freiszel/Nema14-dual-drive-geared-extruder/Images/00_g2d_15_69.png

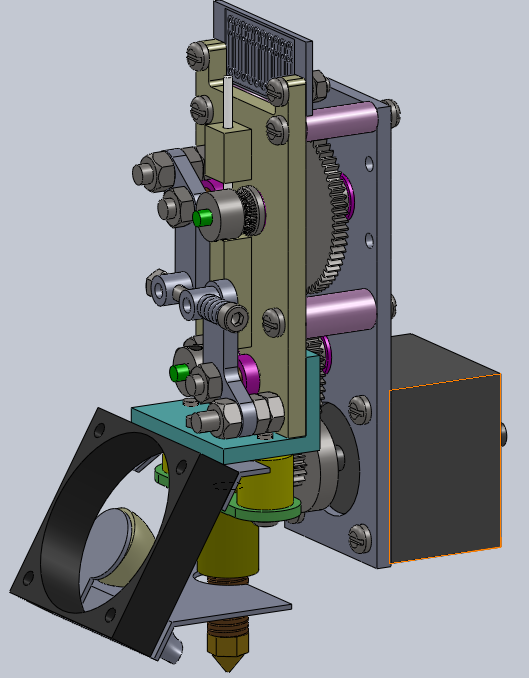
Images/00_g2d_15_69.png
