freiszel/Nema14-dual-drive-geared-extruder/Images/03_GearsMounting.png

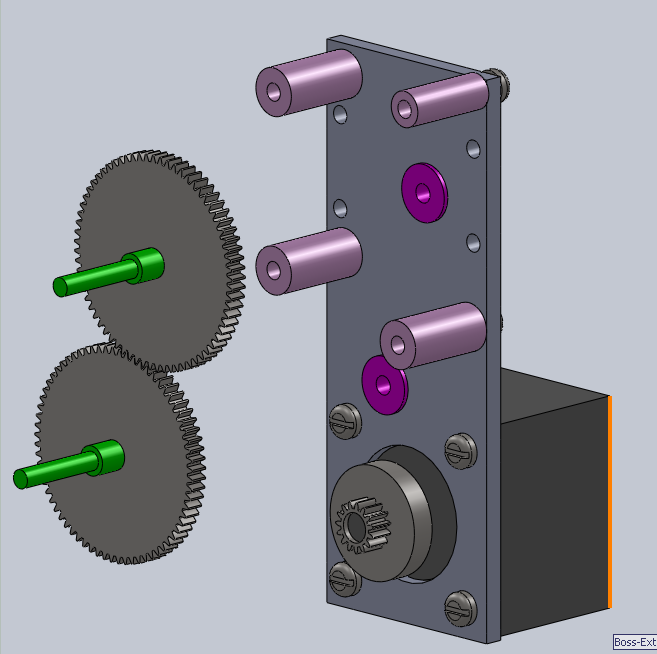
Images/03_GearsMounting.png
