freiszel/Nema14-dual-drive-geared-extruder/Images/04_FrontPlateMounting.png

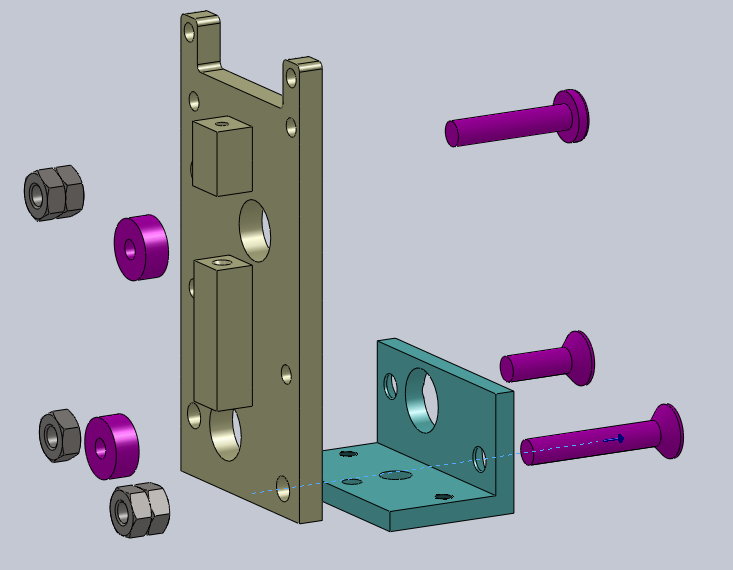
Images/04_FrontPlateMounting.png
