freiszel/Nema14-dual-drive-geared-extruder/Images/05_FrontPlateMounted.png

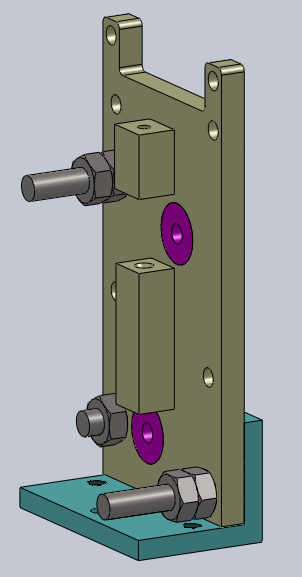
Images/05_FrontPlateMounted.png
