freiszel/Nema14-dual-drive-geared-extruder/Images/06_PressingArmMounting.png

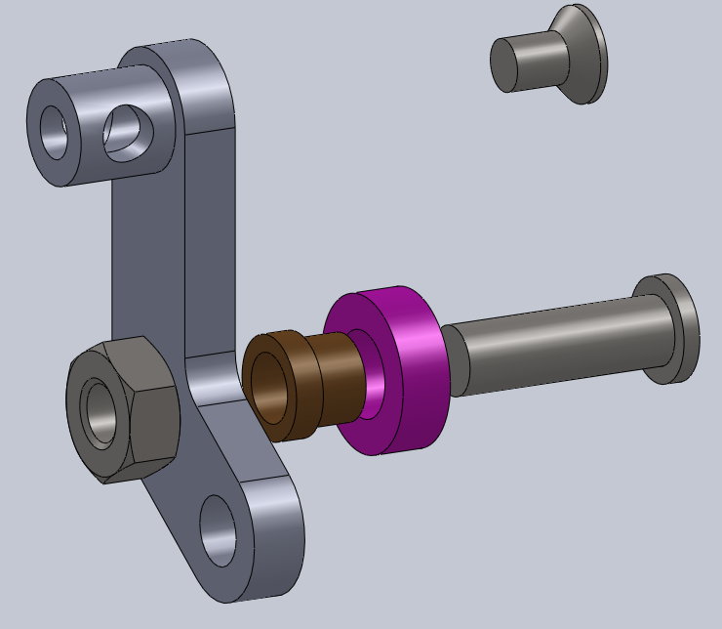
Images/06_PressingArmMounting.png
