freiszel/Nema14-dual-drive-geared-extruder/Images/07_PressingArmMounted.png

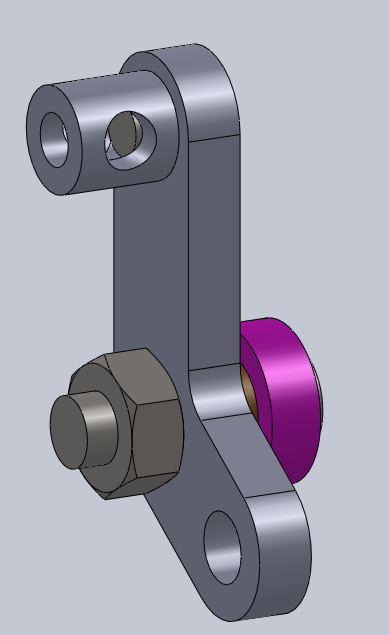
Images/07_PressingArmMounted.png
