freiszel/Nema14-dual-drive-geared-extruder/Images/09_PressingArmsInFrontPanel.png

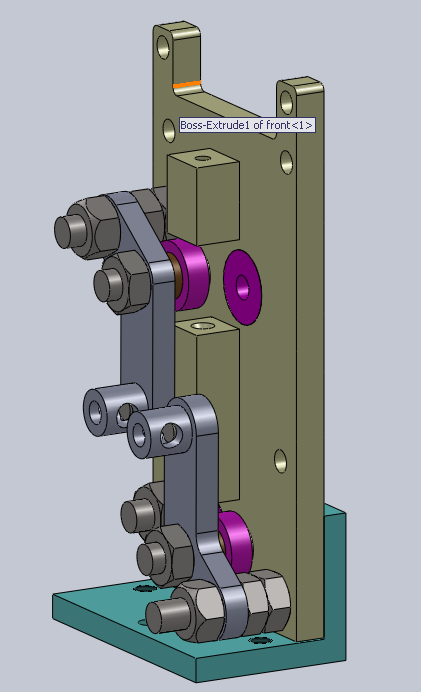
Images/09_PressingArmsInFrontPanel.png
