freiszel/Nema14-dual-drive-geared-extruder/Images/12_DriversAndconectorFixing.png

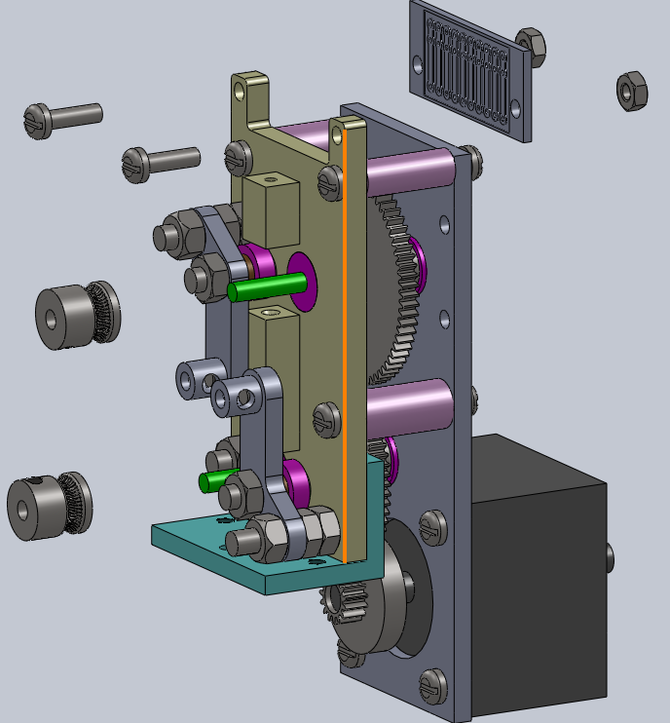
Images/12_DriversAndconectorFixing.png
