freiszel/Nema14-dual-drive-geared-extruder/Images/14_HotendAndPressingScrewMounting.png

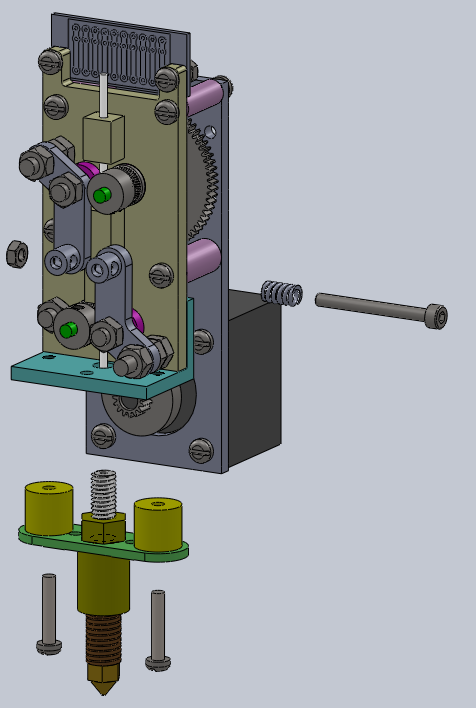
Images/14_HotendAndPressingScrewMounting.png
