freiszel/Nema14-dual-drive-geared-extruder/Images/15_HotendAndPressingScrewMounted.png

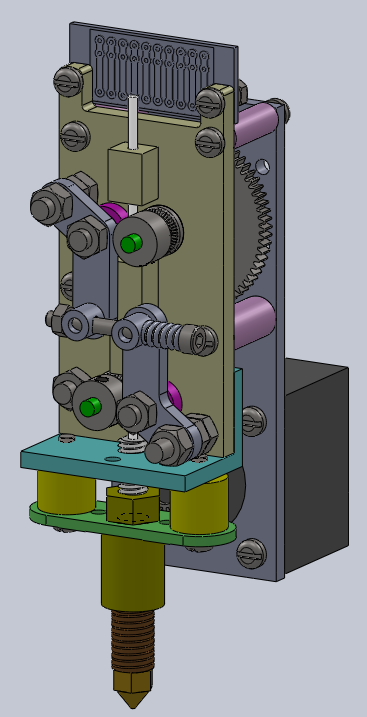
Images/15_HotendAndPressingScrewMounted.png
