freiszel/Nema14-dual-drive-geared-extruder/Images/16_CoolerFixing.png

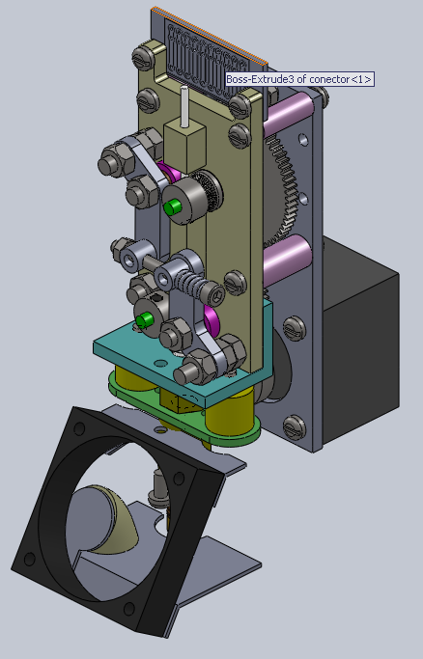
Images/16_CoolerFixing.png
