freiszel/Nema14-dual-drive-geared-extruder/Images/17_CoolerFixed.png

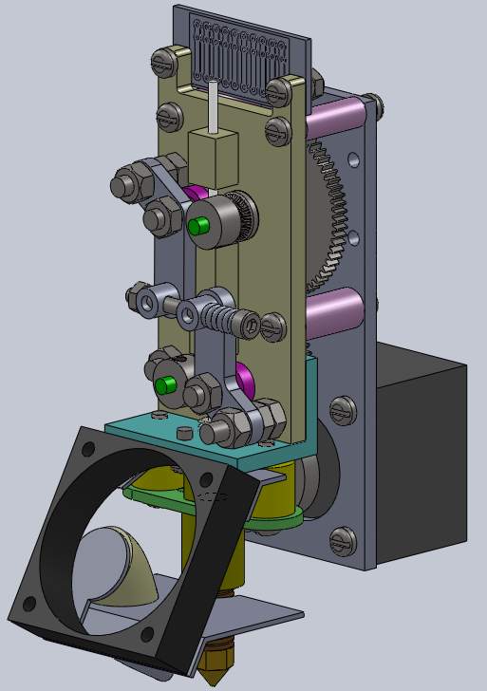
Images/17_CoolerFixed.png
