freiszel/Nema14-dual-drive-geared-extruder/SolidWorks2010/front.SLDPRT

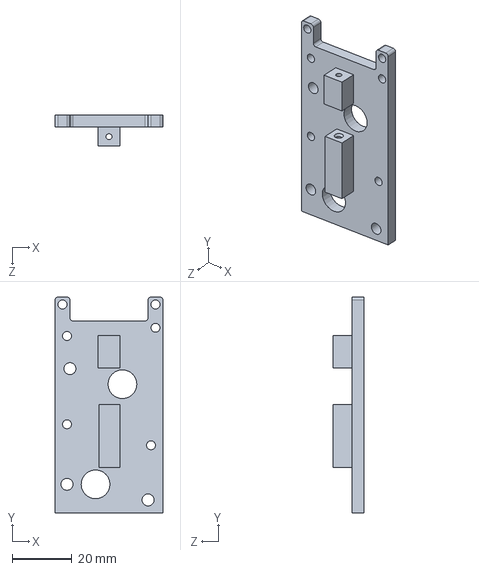
[picture p33: CAD file, 2020-02-22]
SolidWorks2010/front.SLDPRT
36.0 x 72.0 x 10.2 mm
