freiszel/Nema14-dual-drive-geared-extruder/SolidWorks2010/GearN69M05.sldprt

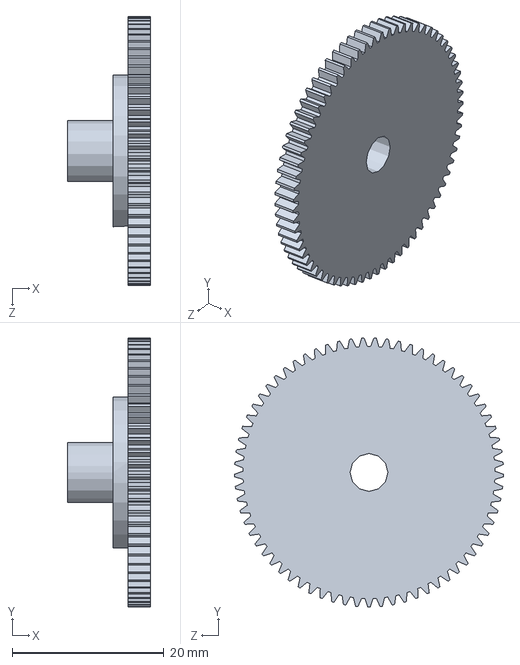
[picture p34: CAD file, 2020-02-22]
SolidWorks2010/GearN69M05.sldprt
11.0 x 35.5 x 35.5 mm
