freiszel/Nema14-dual-drive-geared-extruder/SolidWorks2010/aba.SLDPRT

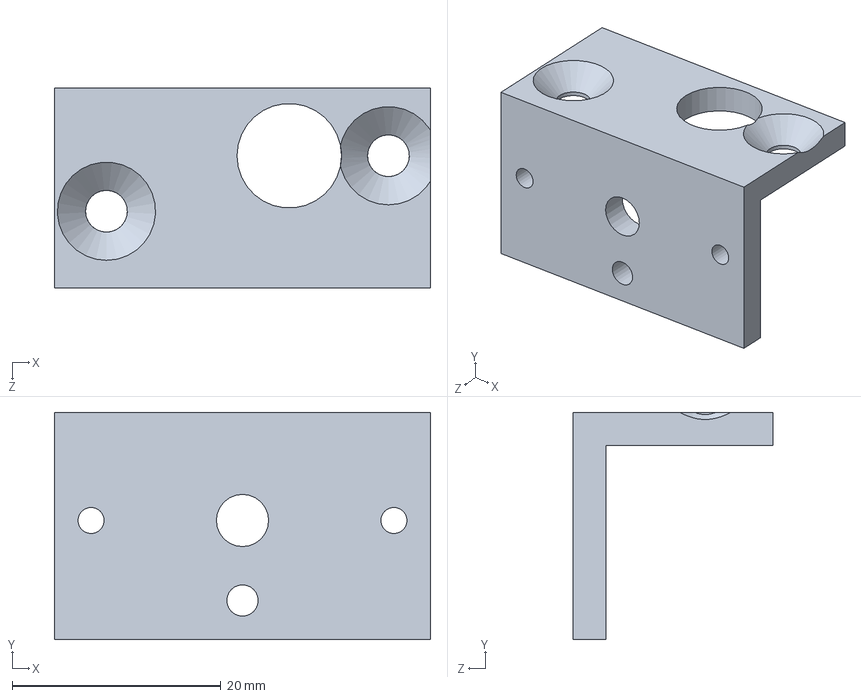
[picture p35: CAD file, 2020-02-22]
SolidWorks2010/aba.SLDPRT
36.0 x 21.7 x 19.2 mm
