freiszel/Nema14-dual-drive-geared-extruder/SolidWorks2010/conector.SLDPRT

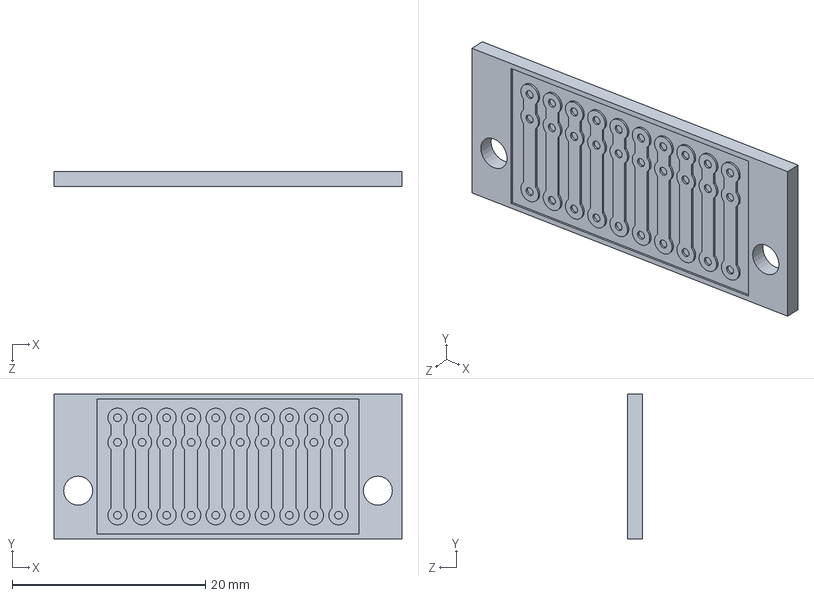
[picture p36: CAD file, 2020-02-22]
SolidWorks2010/conector.SLDPRT
36.0 x 15.0 x 1.50 mm
