freiszel/Nema14-dual-drive-geared-extruder/SolidWorks2010/BrassBush.SLDPRT

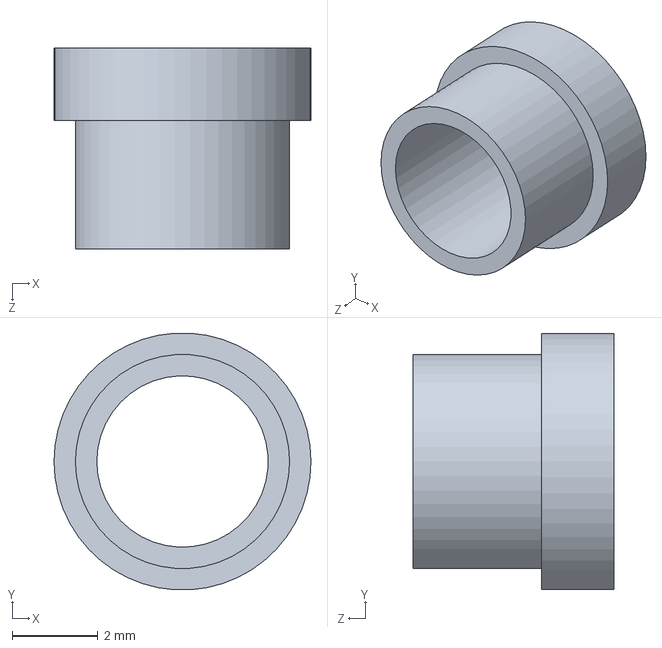
[picture p37: CAD file, 2020-02-22]
SolidWorks2010/BrassBush.SLDPRT
6.00 x 5.99 x 4.70 mm
