freiszel/Nema14-dual-drive-geared-extruder/SolidWorks2010/GearN15M05.sldprt

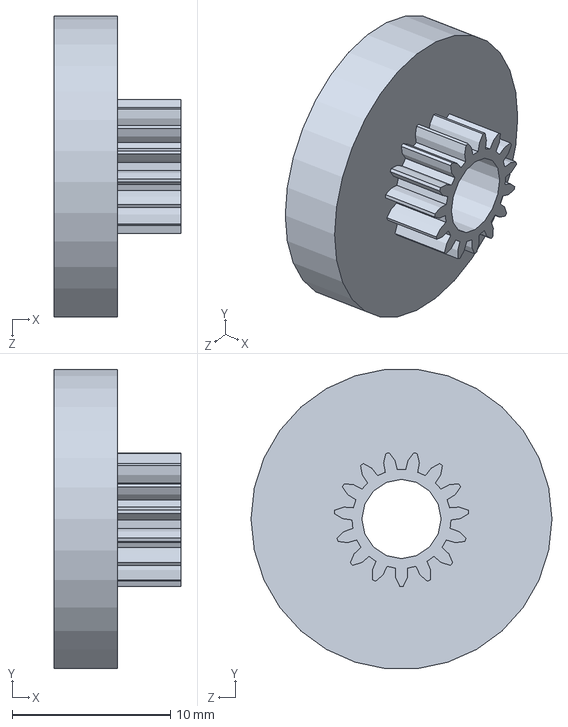
[picture p38: CAD file, 2020-02-22]
SolidWorks2010/GearN15M05.sldprt
8.00 x 18.9 x 19.0 mm
