freiszel/Nema14-dual-drive-geared-extruder/SolidWorks2010/bear 3 16 x x1 8 x 4mm.SLDPRT

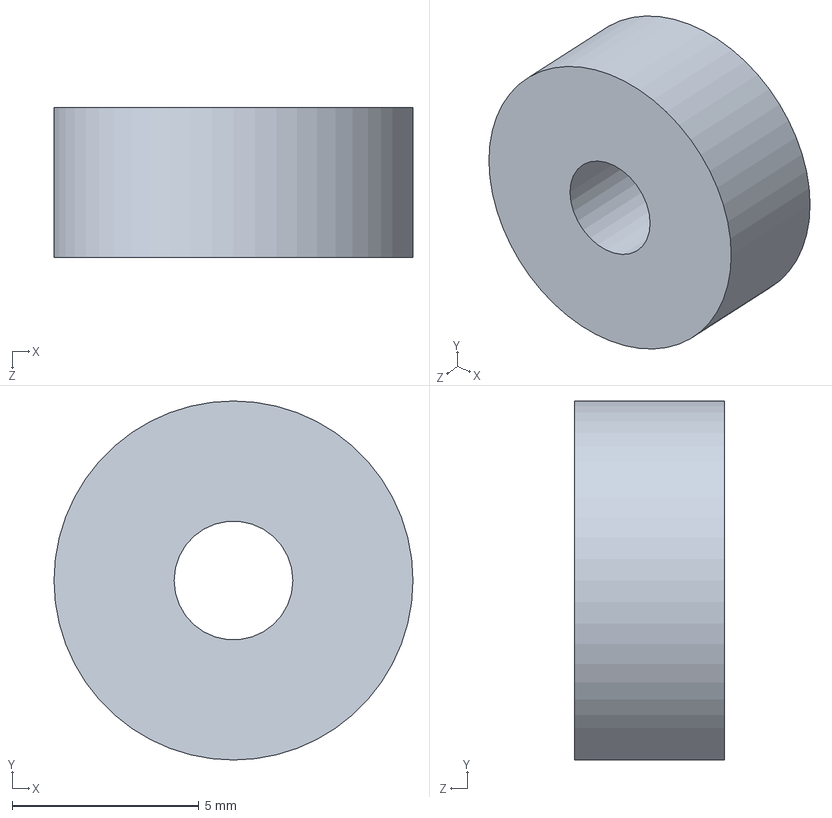
[picture p39: CAD file, 2020-02-22]
SolidWorks2010/bear 3 16 x x1 8 x 4mm.SLDPRT
9.60 x 9.60 x 4.00 mm
